patniemeyer/enclosure/Media/hinge1.jpg

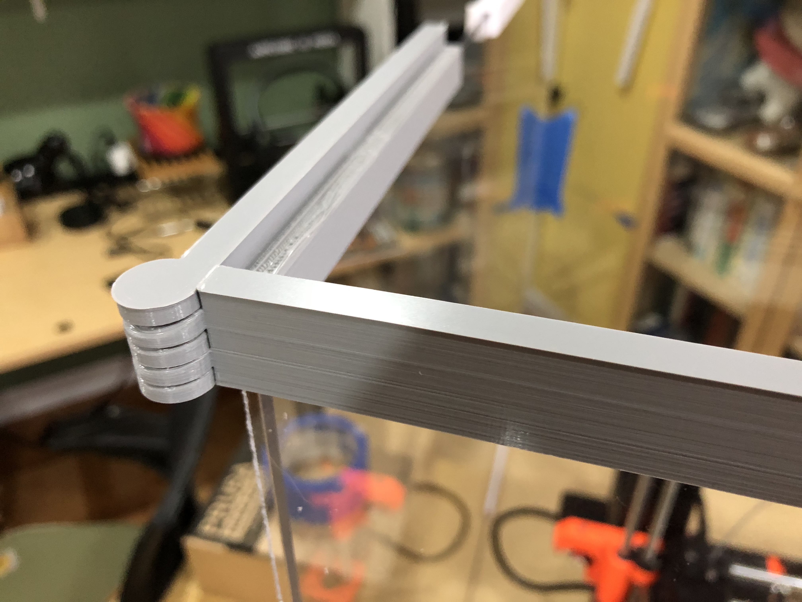
Media/hinge1.jpg
