patniemeyer/enclosure/Media/shot8.png

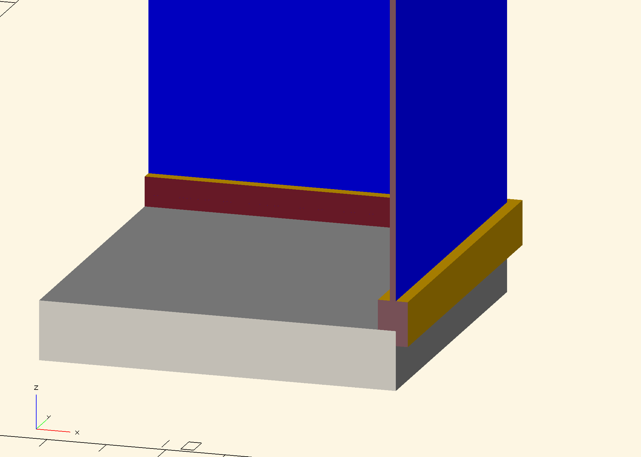
Media/shot8.png
