patniemeyer/enclosure/Media/parts1.jpg

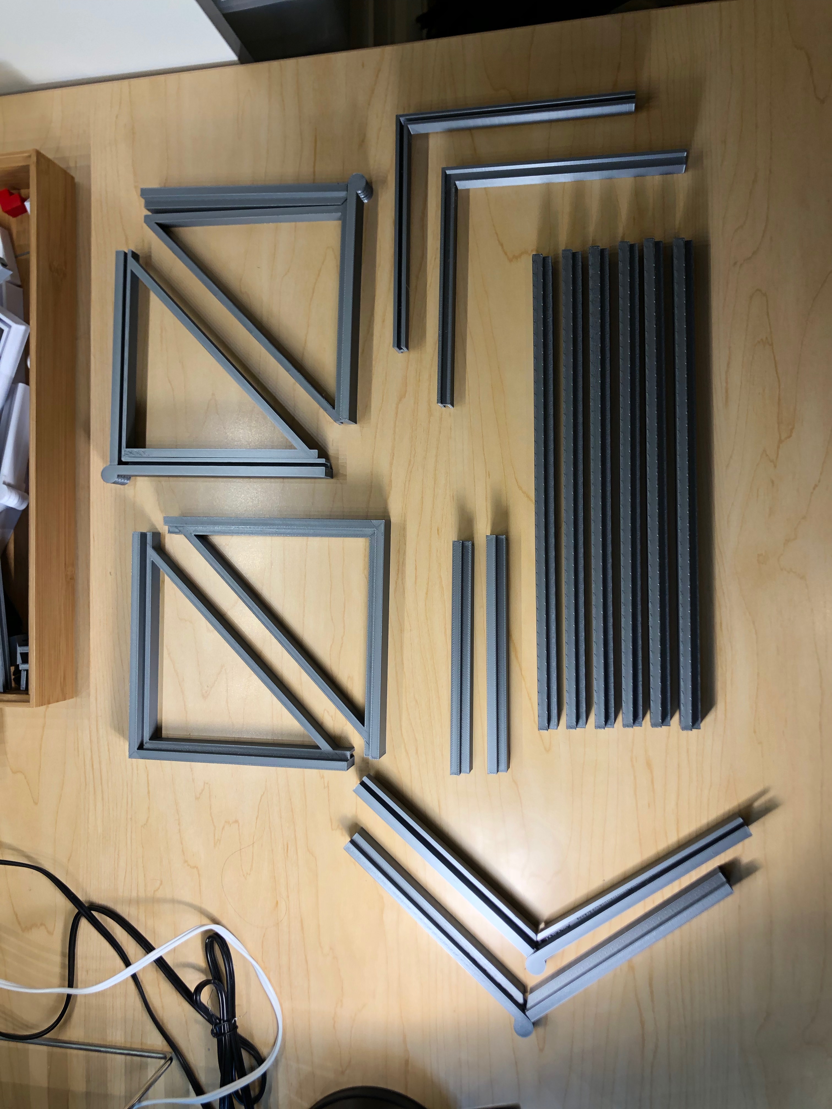
Media/parts1.jpg
