patniemeyer/enclosure/ExperimentsSTL/printer-enclosure17.stl

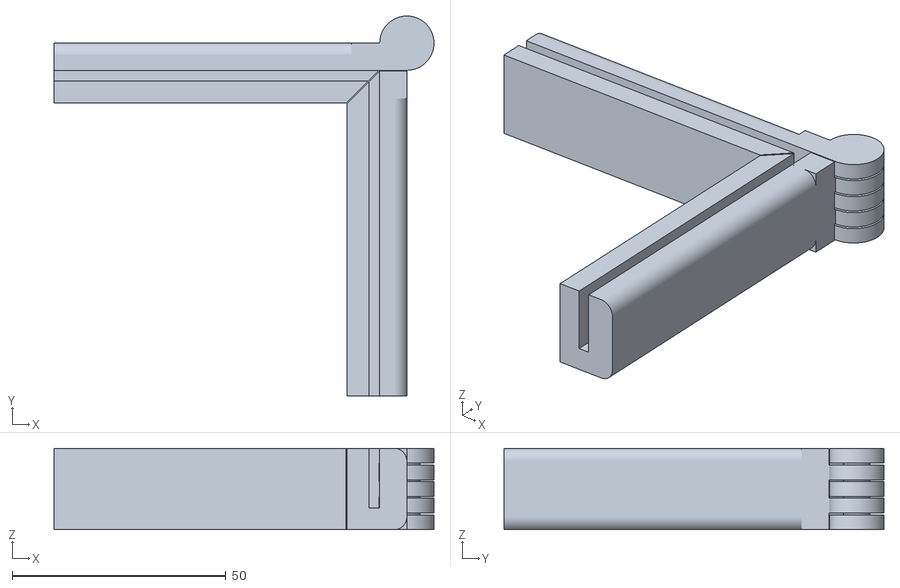
[picture p27: CAD file, 2018-05-16]
ExperimentsSTL/printer-enclosure17.stl
88.9 x 88.9 x 19.1
