patniemeyer/enclosure/ExperimentsSTL/corner1.stl

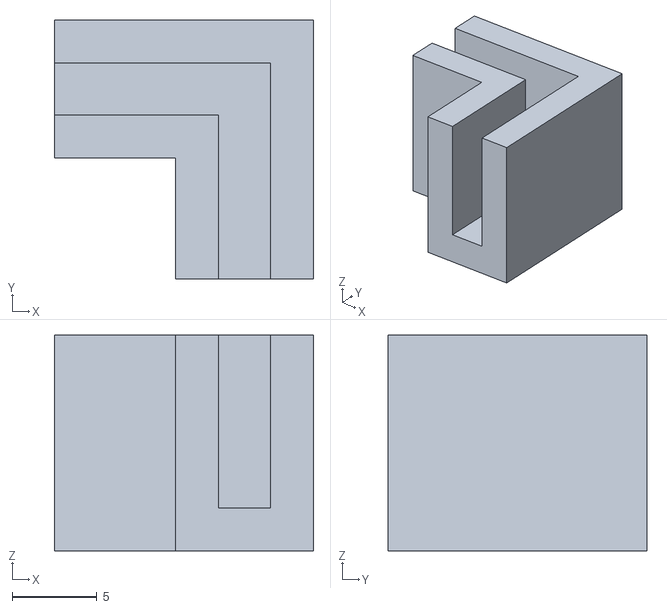
[picture p28: CAD file, 2018-05-16]
ExperimentsSTL/corner1.stl
15.2 x 15.2 x 12.7
