patniemeyer/enclosure/ExperimentsSTL/printer-enclosure7.stl

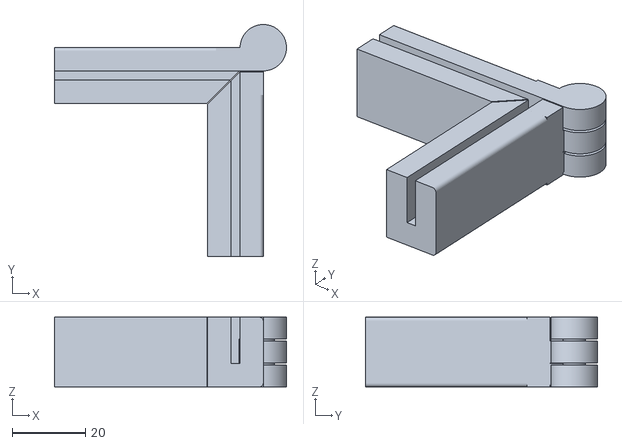
[picture p29: CAD file, 2018-05-16]
ExperimentsSTL/printer-enclosure7.stl
63.5 x 63.5 x 19.1
