patniemeyer/enclosure/ExperimentsSTL/printer-enclosure16.stl

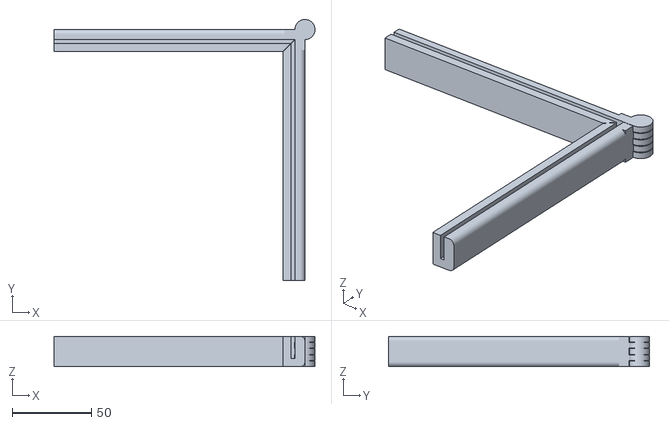
[picture p30: CAD file, 2018-05-16]
ExperimentsSTL/printer-enclosure16.stl
165.1 x 165.1 x 19.1
