patniemeyer/enclosure/ExperimentsSTL/printer-enclosure2.stl

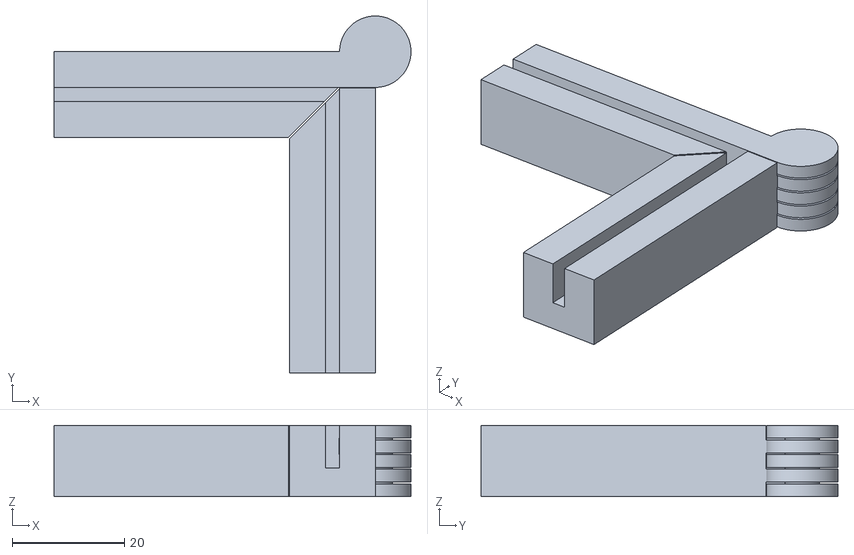
[picture p31: CAD file, 2018-05-16]
ExperimentsSTL/printer-enclosure2.stl
63.5 x 63.5 x 12.7
