patniemeyer/enclosure/ExperimentsSTL/printer-enclosure4.stl

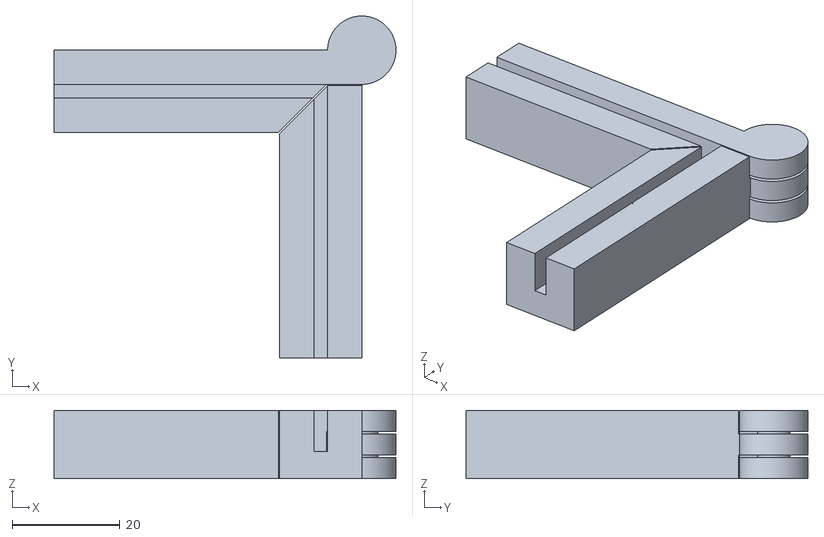
[picture p32: CAD file, 2018-05-16]
ExperimentsSTL/printer-enclosure4.stl
63.5 x 63.5 x 12.7
