patniemeyer/enclosure/ExperimentsSTL/printer-enclosure8.stl

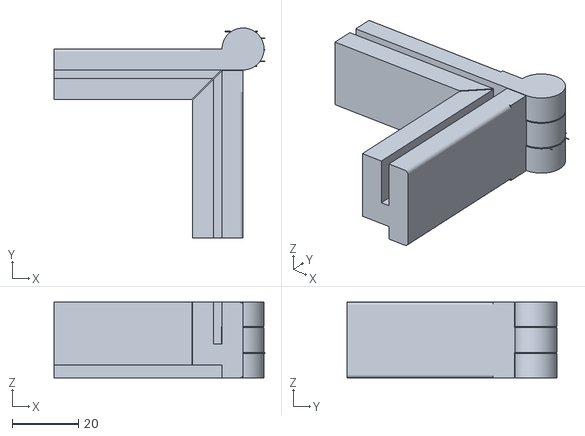
[picture p33: CAD file, 2018-05-16]
ExperimentsSTL/printer-enclosure8.stl
63.8 x 63.5 x 22.9
