patniemeyer/enclosure/ExperimentsSTL/hingetop1.stl

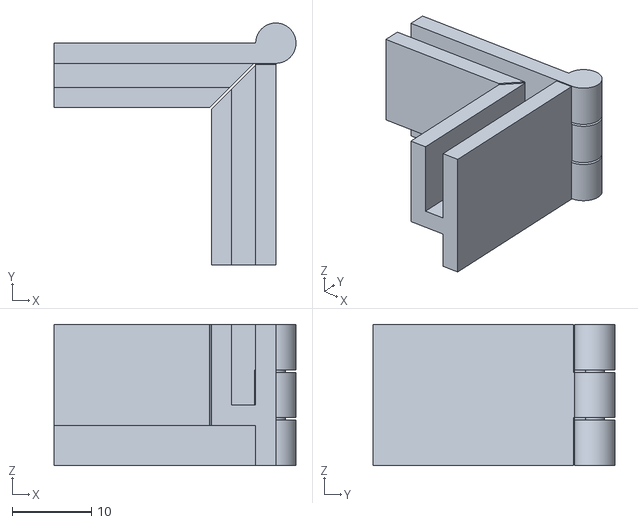
[picture p34: CAD file, 2018-05-16]
ExperimentsSTL/hingetop1.stl
30.5 x 30.5 x 17.8
