patniemeyer/enclosure/ExperimentsSTL/printer-enclosure12.stl

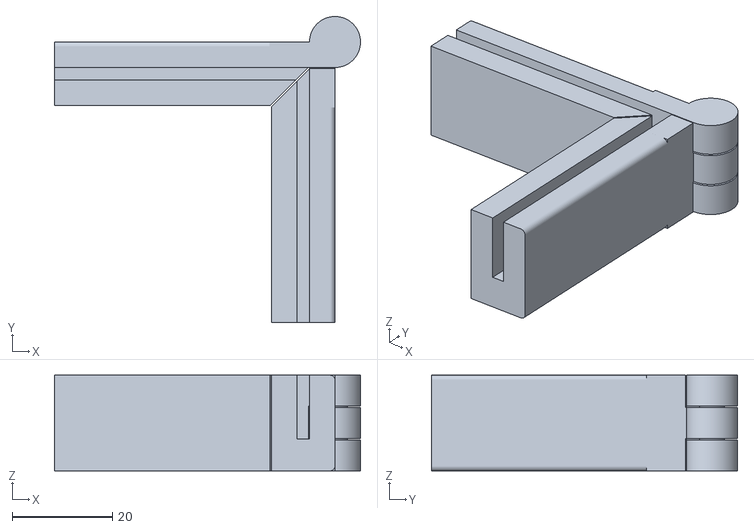
[picture p35: CAD file, 2018-05-16]
ExperimentsSTL/printer-enclosure12.stl
61.0 x 61.0 x 19.1
